tnpp712/cc_hud_esp32/firmware/src/lvgl_ui.h

// lvgl_ui.h
// LVGL 9 user interface for cc_hud — replaces the legacy hand-drawn
// renderer for the HUD and idle screens. The OTA progress screen stays
// on the legacy Adafruit path in display.cpp (LVGL stops ticking while
// OTA owns the panel; the device reboots after).
//
// Data flow: main.cpp stays the owner of all state. Once per loop it
// fills an LvglUiModel and calls lvglUiApply(); widget updates happen
// only where values actually changed. lvglUiTick() pumps LVGL timers.

#pragma once


#include <Arduino.h>

#include "config.h"
#include "persistence.h"
#include "v7_tlv.h"   // V7Session(第 4 层会话列表)

namespace cc_hud {

struct LvglUiModel {
    QuotaSnapshot quota;          // latest quota + idle-time fields
    bool          ble_connected = false;
    bool          idle_mode     = false;   // true → clock screen
    AppState      app_state     = kAppStateUnset;
    char          app_detail[kAppStateDetailMaxLen + 1] = {0};
    uint8_t       total_sessions = 0;  // stage 3: live Claude Code sessions
    uint8_t       busy_sessions  = 0;  // stage 3: how many are non-idle
    uint8_t       app_intervention = 0;  // 介入类型(waiting 时):0=none 1=approval 2=question 3=error
    uint8_t       session_count    = 0;          // 第 4 层:会话列表条数
    V7Session     sessions[kMaxV7Sessions];      // 按优先级排序(等你的在前)
    // Burn-rate prediction (computed in main.cpp). When exhaust_warn is set,
    // the named window is projected to hit 100% BEFORE it resets.
    bool          exhaust_warn   = false;
    uint8_t       exhaust_which  = 0;   // 0 = 5h window, 1 = 7d window
    uint32_t      exhaust_eta_s  = 0;   // seconds until projected exhaustion
    // Optional battery monitor. battery_pct == 255 means "no sensor wired".
    uint8_t       battery_pct    = 255;
    bool          battery_low    = false;
    PetMood       mood          = kPetMoodHappy;
    uint64_t      now_ms        = 0;
};

// Bring up LVGL (tick source, display driver, both screens, assets).
// Call once from setup(), after displayInit().
void lvglUiInit();

// Pump LVGL timers/refresh. Call every loop() iteration.
void lvglUiTick();

// Diff the model against the on-screen state and update widgets.
// Cheap when nothing changed; call every loop() iteration.
void lvglUiApply(const LvglUiModel& m);

// One-shot red alert flash (non-blocking; ~5 s of pulsing overlay).
void lvglUiFlashAlert();

// Manually jump to the next page (button short-press). Holds that page for
// a few seconds, then the auto-carousel / activity logic resumes.
void lvglUiManualAdvance();

}  // namespace cc_hud
